brickbots/framedeck/images/DSC_0325.jpeg

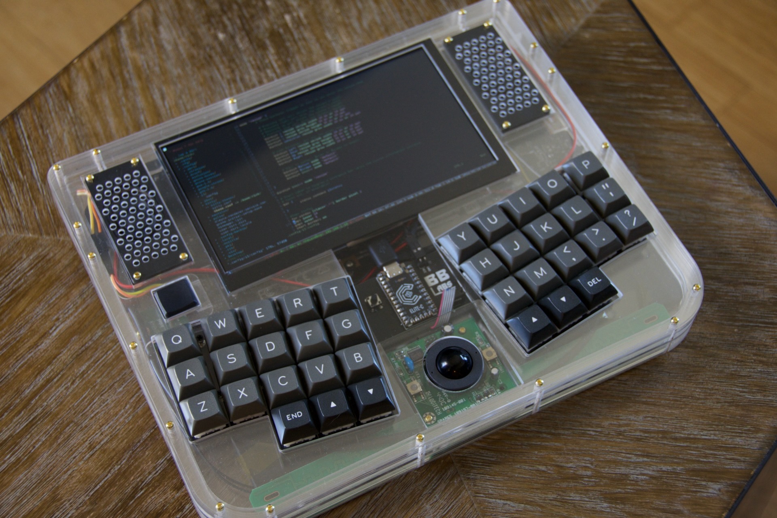
images/DSC_0325.jpeg
