brickbots/framedeck/images/DSC_0326.jpeg

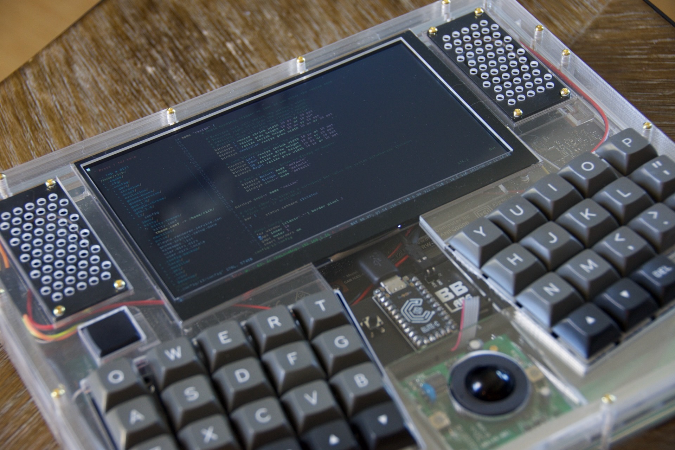
images/DSC_0326.jpeg
