brickbots/framedeck/images/DSC_0351.jpeg

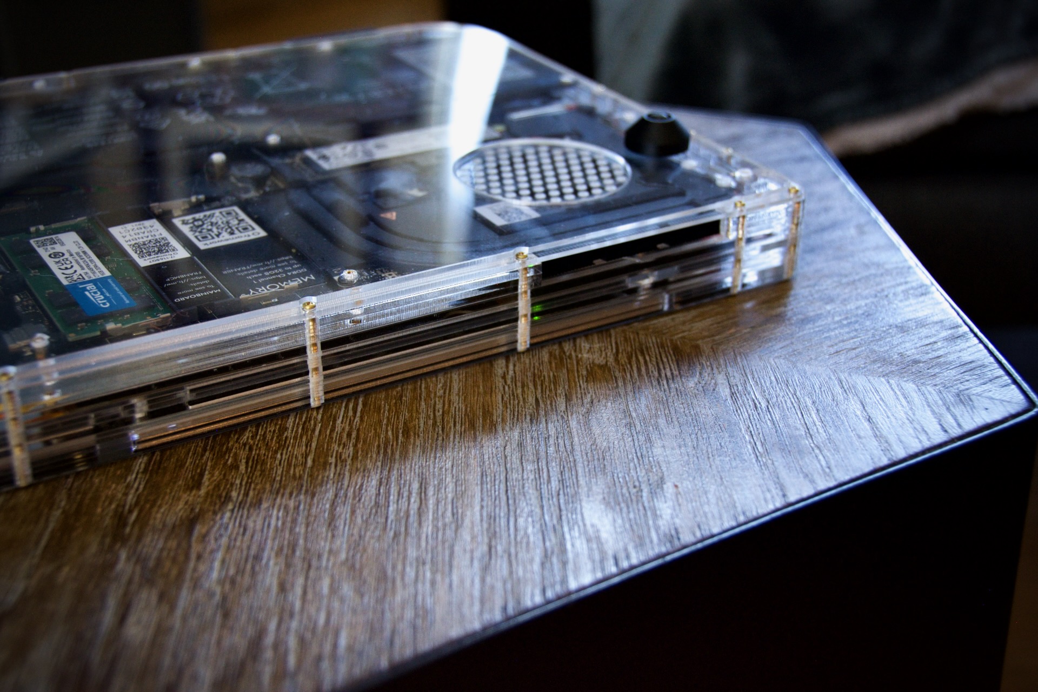
images/DSC_0351.jpeg
