brickbots/framedeck/images/DSC_0352.jpeg

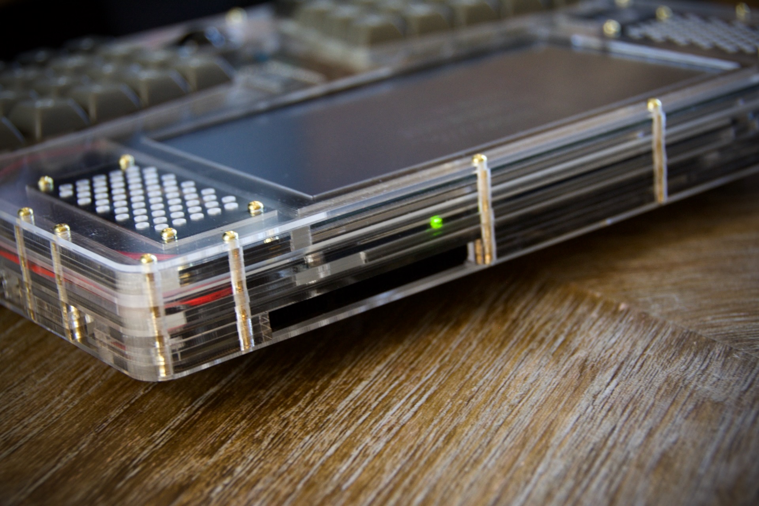
images/DSC_0352.jpeg
