brickbots/framedeck/images/DSC_0357.jpeg

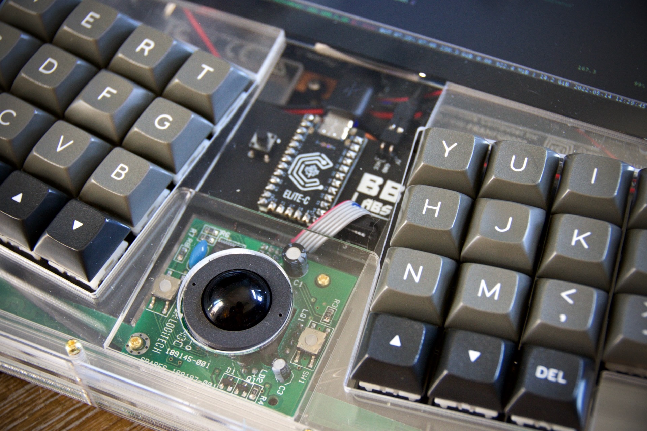
images/DSC_0357.jpeg
