brickbots/framedeck/images/DSC_0416.jpeg

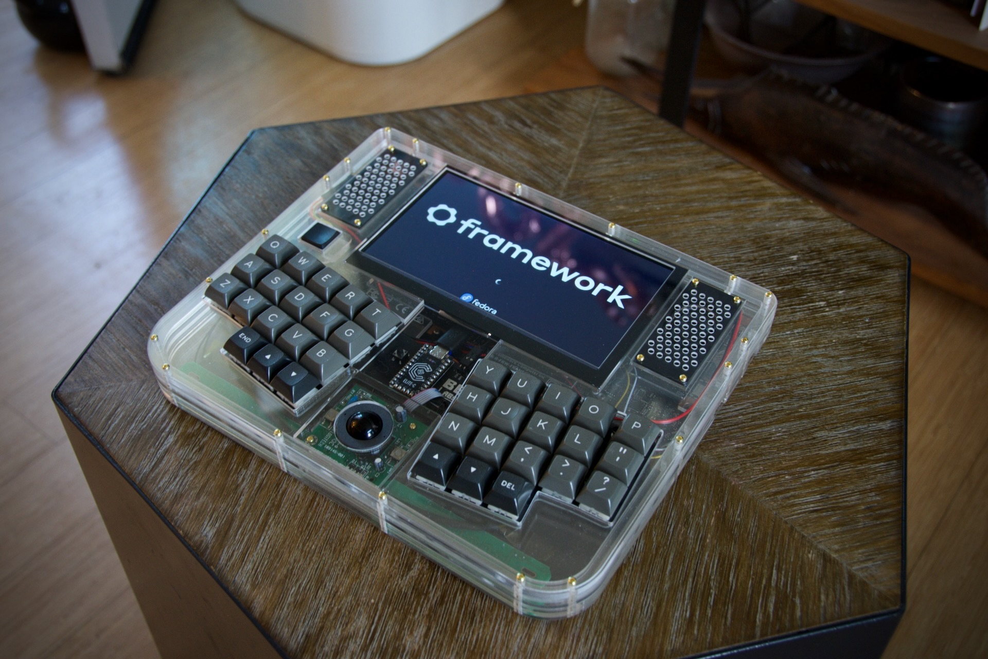
images/DSC_0416.jpeg
