brickbots/framedeck/case/framedeck_case_EG.dxf

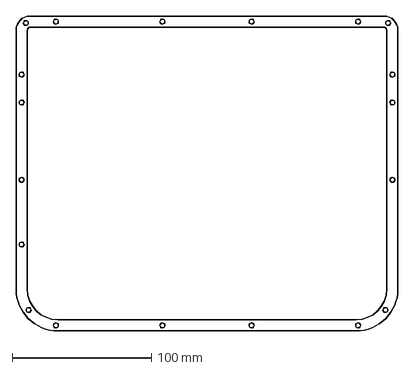
[picture p38: CAD file, 2022-05-11]
case/framedeck_case_EG.dxf
274.0 x 226.0 mm
