brickbots/framedeck/case/framedeck_case_H.dxf

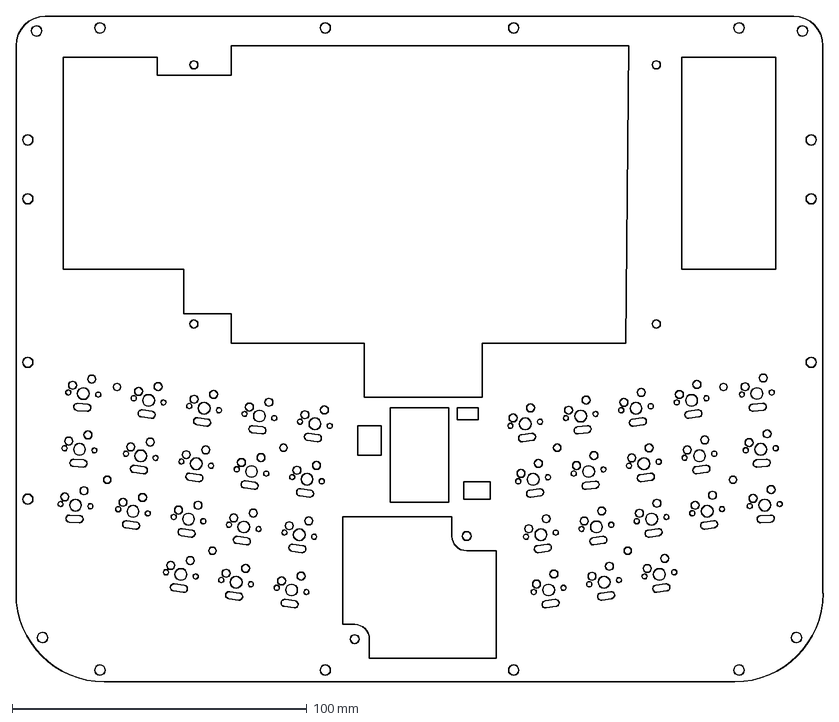
[picture p39: CAD file, 2022-05-11]
case/framedeck_case_H.dxf
274.0 x 226.0 mm
