brickbots/framedeck/case/framedeck_case_J2.dxf

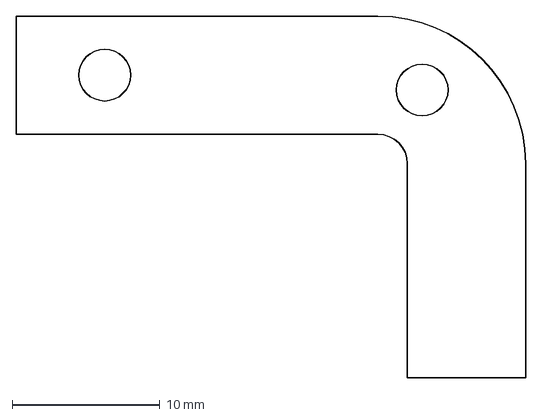
[picture p40: CAD file, 2022-05-11]
case/framedeck_case_J2.dxf
34.5 x 24.5 mm
