brickbots/framedeck/case/framedeck_case_C.dxf

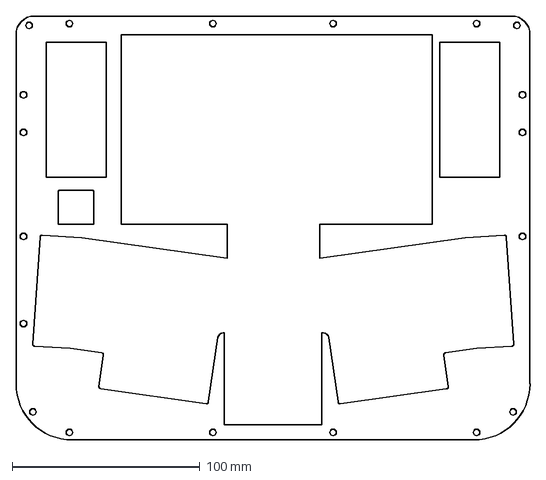
[picture p41: CAD file, 2022-05-11]
case/framedeck_case_C.dxf
274.0 x 226.0 mm
