brickbots/framedeck/case/framedeck_case_J3.dxf

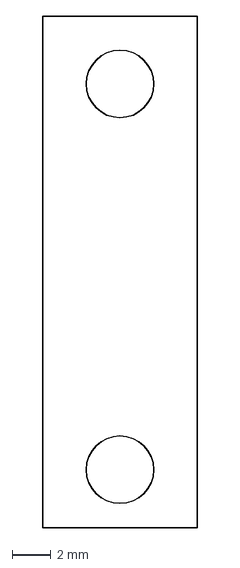
[picture p42: CAD file, 2022-05-11]
case/framedeck_case_J3.dxf
8.00 x 26.5 mm
